MechatronikMonkey/Wechselbalg50/mechanics/Shild.step

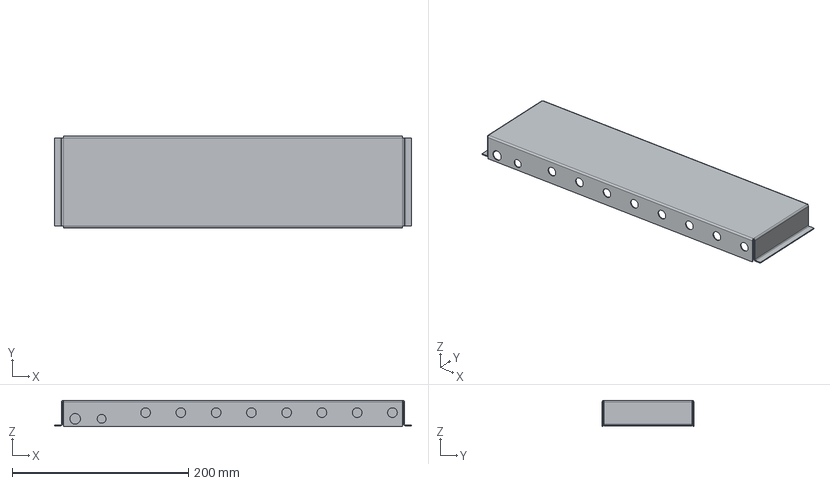
[picture p17: CAD file, 2025-10-03]
mechanics/Shild.step
405.0 x 104.0 x 30.0 mm
