MechatronikMonkey/Wechselbalg50/electronics/shared_libraries/3dmodels/12ax7.STEP

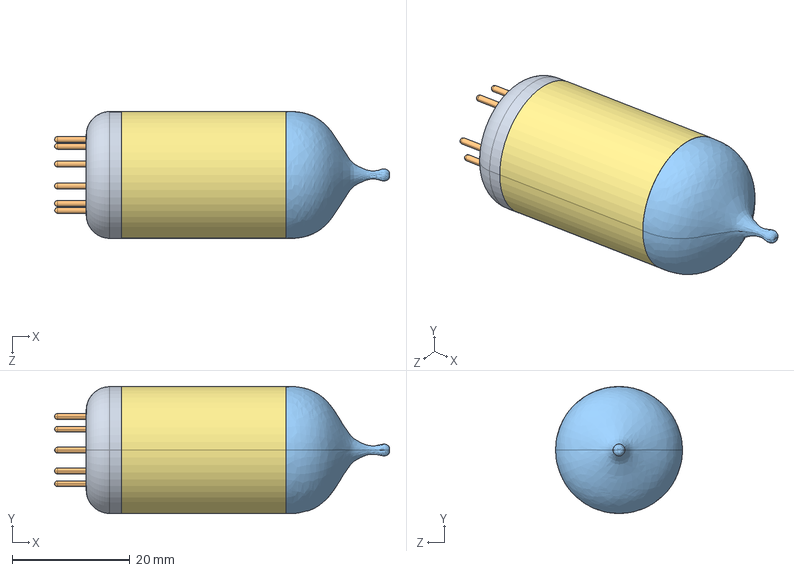
[picture p18: CAD file, 2025-09-29]
electronics/shared_libraries/3dmodels/12ax7.STEP
56.9 x 21.6 x 21.5 mm
Cópia de chapeu-dissipador^final
suporte-dissipador
dissipador
cintura baixa x 2
coluna-cintura-baixa x 2
anodos x 2
caulda da base
base-vidro-corpo
terminais x 9
corpo-topo
terminais-internos x 3
terminais-lamina
terminais-filamentos x 5
corpo-vidro-meio
