MechatronikMonkey/Wechselbalg50/mechanics/Ubertrager.FCStd

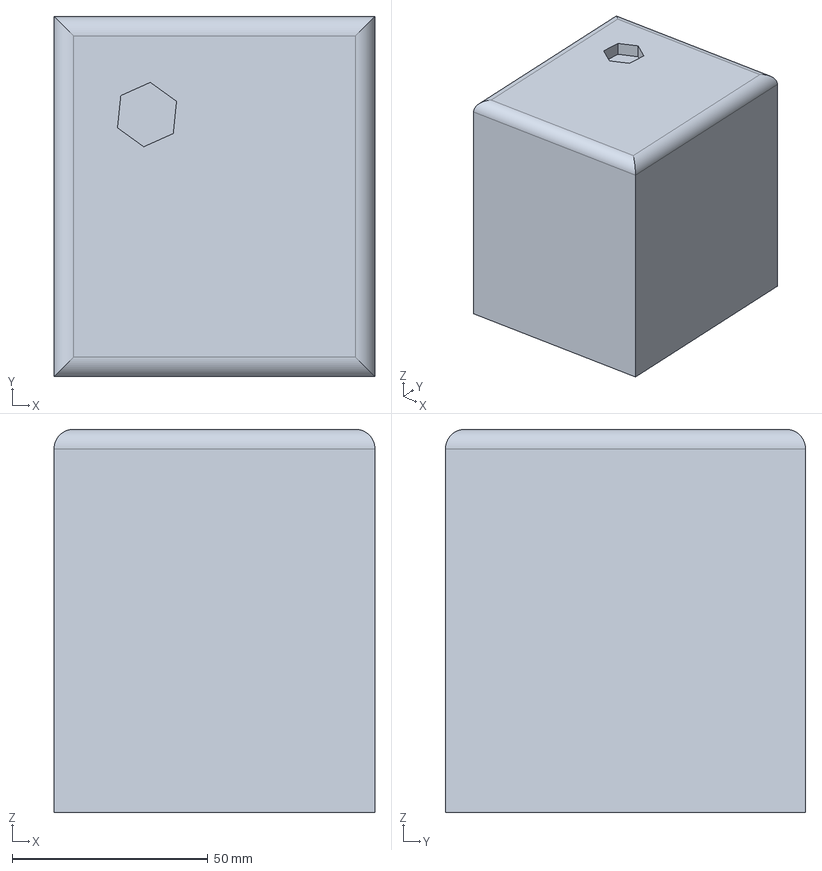
[picture p19: CAD file, 2025-09-30]
mechanics/Ubertrager.FCStd
82.0 x 92.0 x 98.0 mm
