MechatronikMonkey/Wechselbalg50/electronics/shared_libraries/3dmodels/ACJS-PH v28.step

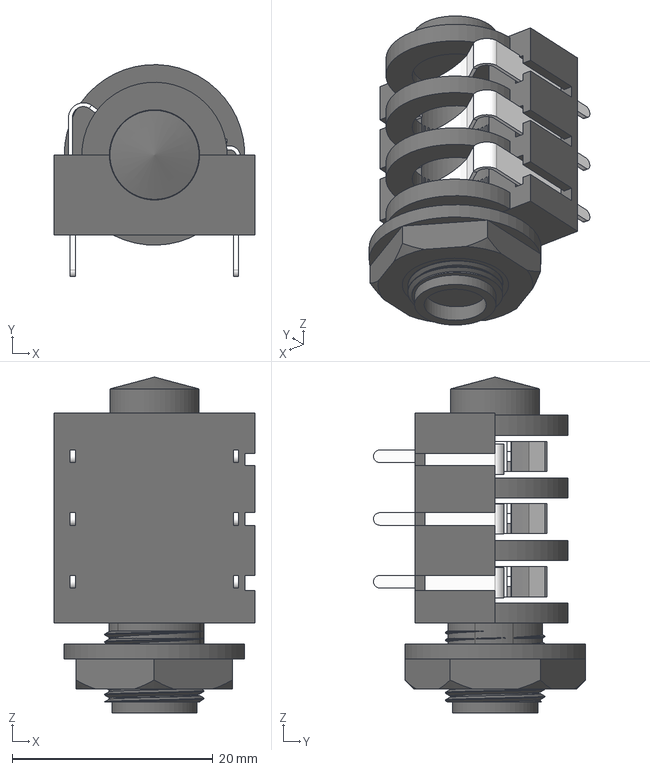
[picture p20: CAD file, 2025-09-27]
electronics/shared_libraries/3dmodels/ACJS-PH v28.step
20.0 x 21.1 x 33.5 mm
JackConnector-female-6.35-entrance-threaded
nut
