MechatronikMonkey/Wechselbalg50/mechanics/Drossel.FCStd

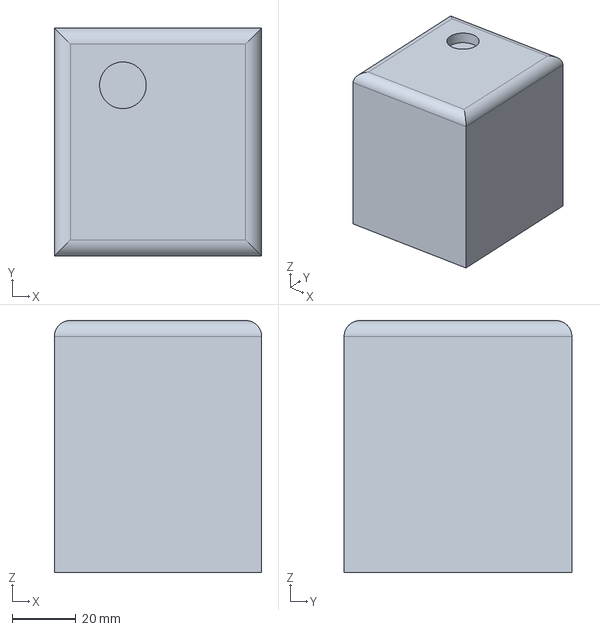
[picture p21: CAD file, 2025-09-30]
mechanics/Drossel.FCStd
65.0 x 71.4 x 79.0 mm
