MechatronikMonkey/Wechselbalg50/electronics/shared_libraries/3dmodels/PC20BU.stp

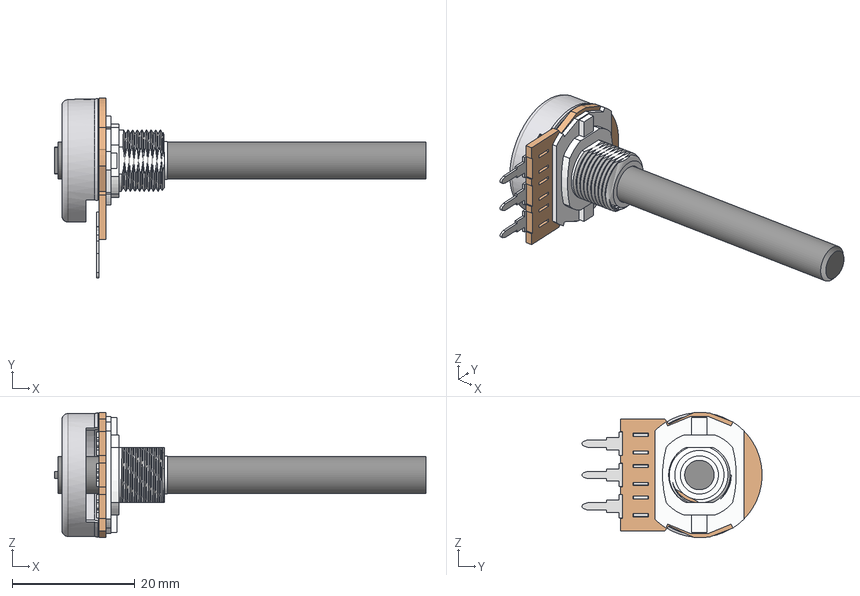
[picture p22: CAD file, 2025-09-27]
electronics/shared_libraries/3dmodels/PC20BU.stp
61.0 x 29.3 x 20.4 mm
