MechatronikMonkey/Wechselbalg50/mechanics/Transformer.FCStd

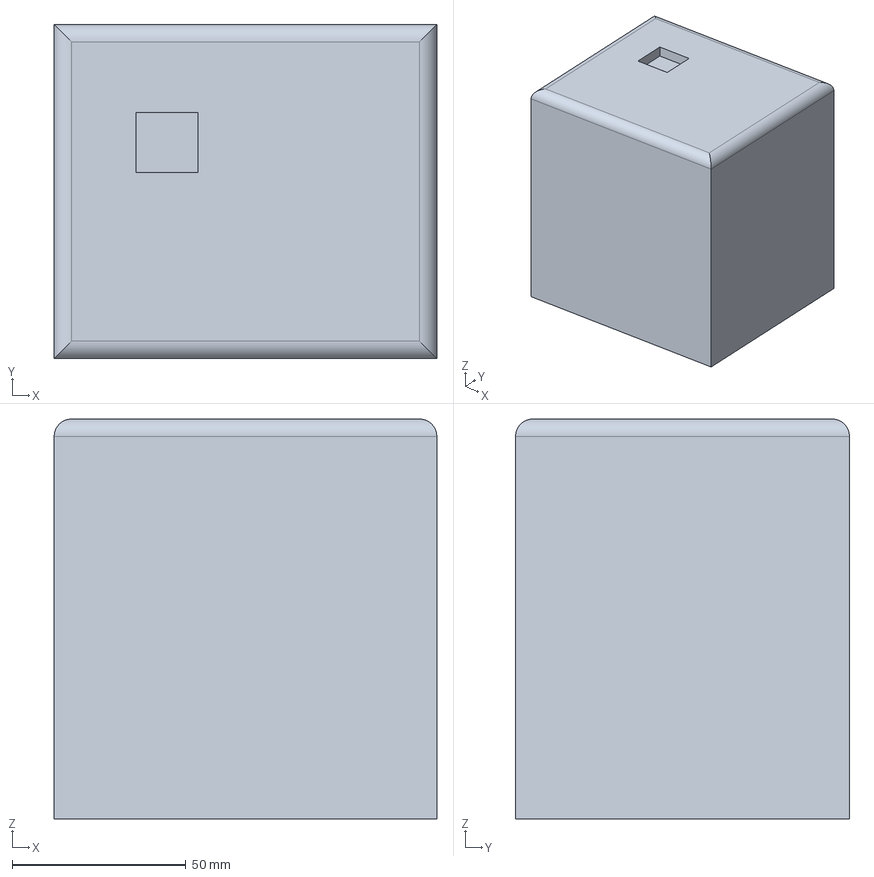
[picture p23: CAD file, 2025-09-30]
mechanics/Transformer.FCStd
110.0 x 96.0 x 115.0 mm
